quintinbannink42/hellen-pdm-razor/scripts/adio_rest_blockers.png

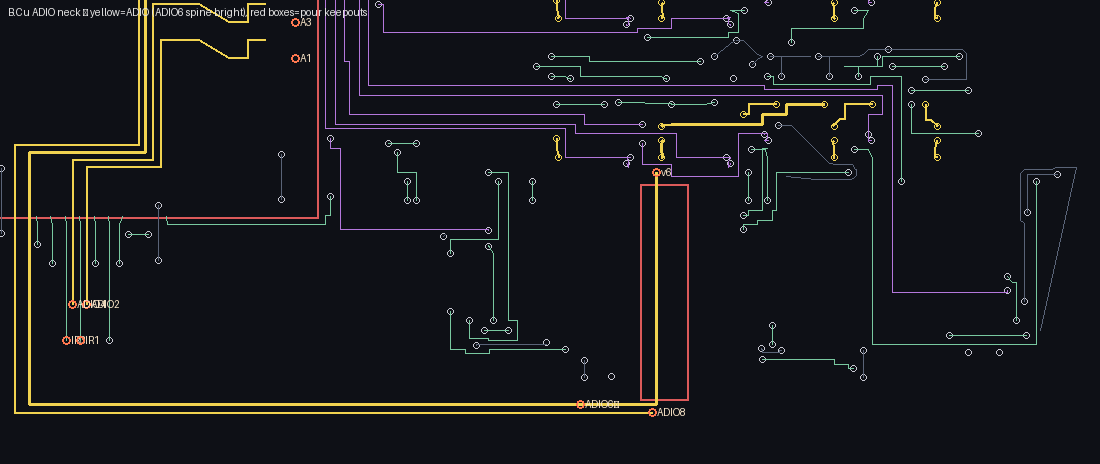
scripts/adio_rest_blockers.png
