quintinbannink42/hellen-pdm-razor/scripts/r10_stitch.png

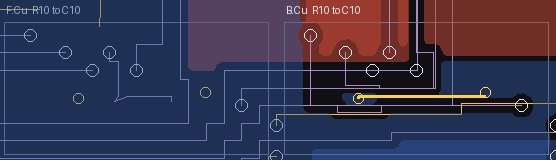
scripts/r10_stitch.png
